felipebalbi/pico-de-gallo/book/src/SUMMARY.md

# Summary

- [Introduction](./introduction.md)
- [Getting Started](./getting-started.md)
- [Gallo Crates](./gallo-crates.md)
- [GPIO](./gpio.md)
- [UART](./uart.md)
- [PWM](./pwm.md)
- [ADC](./adc.md)
- [Transaction Batching](./transaction-batching.md)
- [1-Wire Bus](./onewire.md)
- [FFI / C Bindings](./ffi.md)
- [Writing A Device Driver](./driver.md)
