felipebalbi/pico-de-gallo/crates/pico-de-gallo-lib/src/decode.rs

//! Host-side protocol decoders for raw capture data.
//!
//! These decoders operate on the raw sample stream produced by the logic capture
//! subsystem. Each sample is one byte where bit N represents the state of capture
//! channel N.
//!
//! Both decoders are **stateful** and **iterator-based**: call [`I2cDecoder::feed`]
//! or [`UartDecoder::feed`] with each chunk of samples. The returned iterator
//! yields decoded frames/bytes. State is preserved across calls so a protocol
//! transaction can span multiple chunks.
//!
//! # Example
//!
//! ```rust,no_run
//! use pico_de_gallo_lib::decode::{I2cDecoder, I2cFrame};
//!
//! let mut decoder = I2cDecoder::new(0, 1, 500_000);
//! // ... receive samples from capture subscription ...
//! # let samples: &[u8] = &[];
//! for frame in decoder.feed(samples) {
//!     println!("{frame:?}");
//! }
//! ```

use std::fmt;

// ---------------------------------------------------------------------------
// I2C Decoder
// ---------------------------------------------------------------------------

/// A decoded I2C bus event.
#[derive(Debug, Clone, PartialEq, Eq)]
pub enum I2cFrame {
    /// START condition (SDA falls while SCL is high).
    Start {
        /// Sample index within the capture stream.
        sample_index: u64,
    },
    /// Repeated START condition.
    RepeatedStart {
        /// Sample index within the capture stream.
        sample_index: u64,
    },
    /// STOP condition (SDA rises while SCL is high).
    Stop {
        /// Sample index within the capture stream.
        sample_index: u64,
    },
    /// A complete byte (8 data bits + ACK/NACK).
    Data {
        /// The decoded byte value.
        value: u8,
        /// `true` if the receiver acknowledged (SDA low on 9th clock).
        ack: bool,
        /// Sample index of the first bit.
        sample_index: u64,
    },
}

impl fmt::Display for I2cFrame {
    fn fmt(&self, f: &mut fmt::Formatter<'_>) -> fmt::Result {
        match self {
            Self::Start { sample_index } => write!(f, "[S @{sample_index}]"),
            Self::RepeatedStart { sample_index } => write!(f, "[Sr @{sample_index}]"),
            Self::Stop { sample_index } => write!(f, "[P @{sample_index}]"),
            Self::Data {
                value,
                ack,
                sample_index,
            } => {
                let ack_str = if *ack { "A" } else { "N" };
                write!(f, "[0x{value:02X} {ack_str} @{sample_index}]")
            }
        }
    }
}
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
